Aiano/LocateMagnet/Hardware/114514/PIC/114514.png

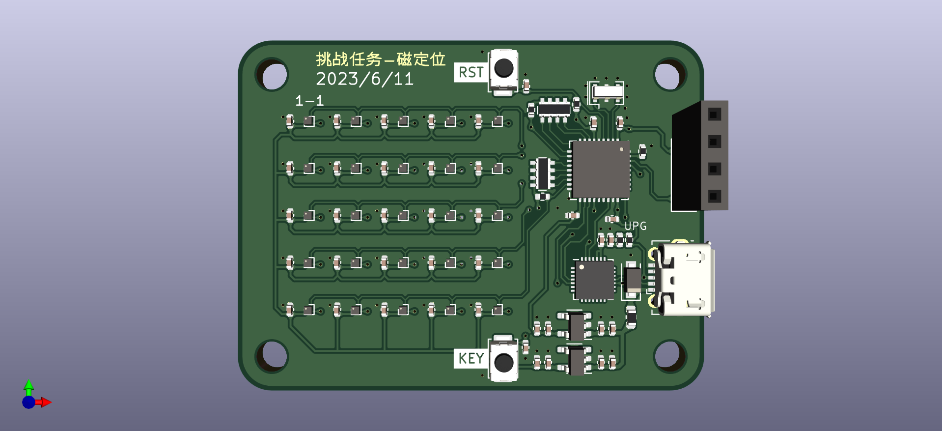
Hardware/114514/PIC/114514.png
