Aiano/LocateMagnet/Hardware/114514/PIC/1145141.png

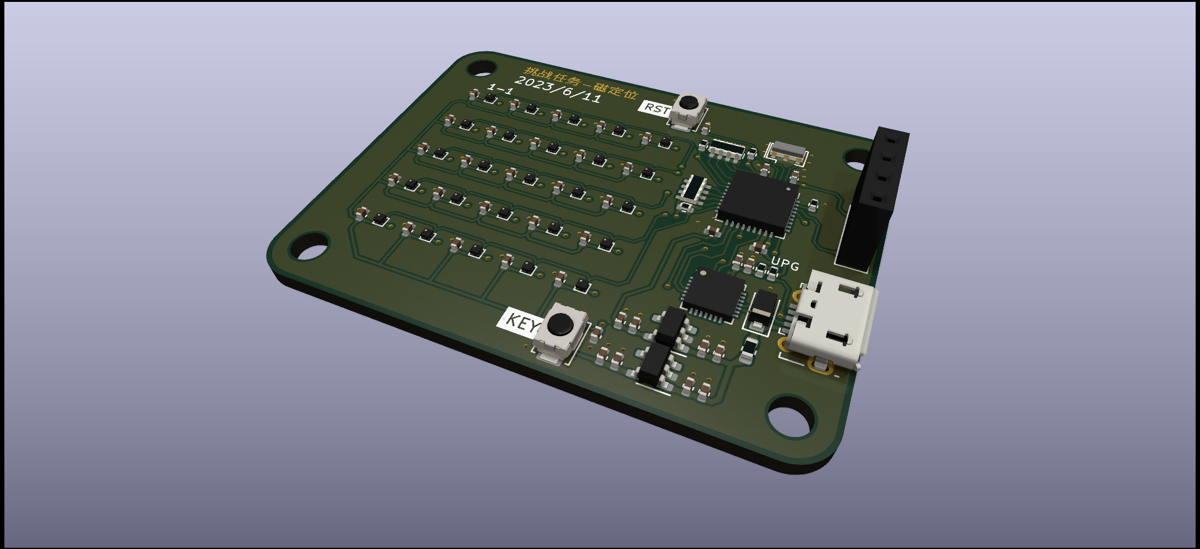
Hardware/114514/PIC/1145141.png
