Aiano/LocateMagnet/Result/反向.png

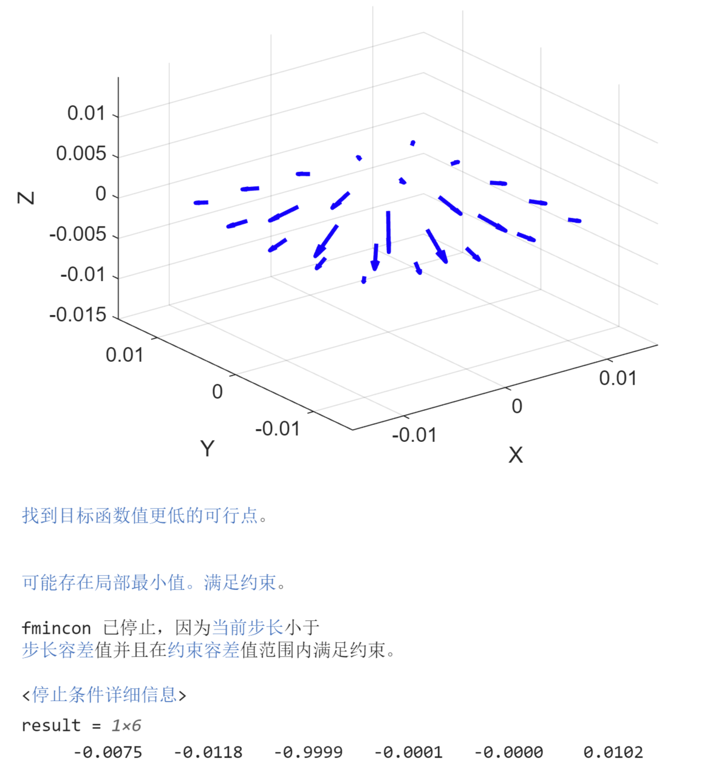
Result/反向.png
