Aiano/LocateMagnet/Result/反向摆放.jpg

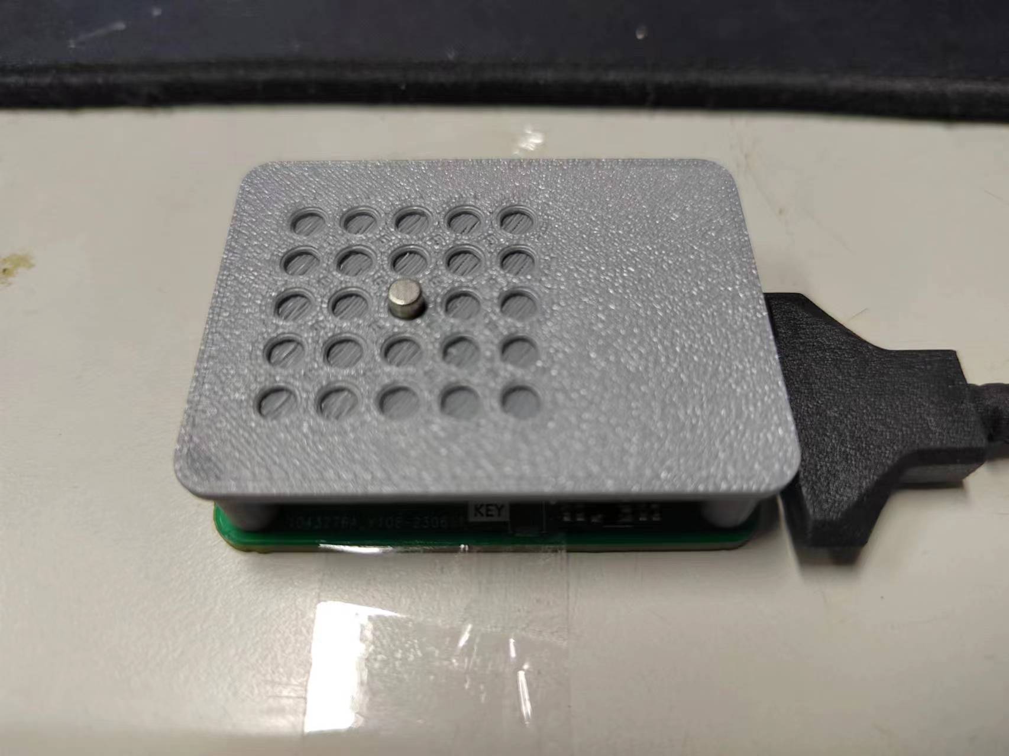
Result/反向摆放.jpg
