Aiano/LocateMagnet/Result/右移0.5mm.png

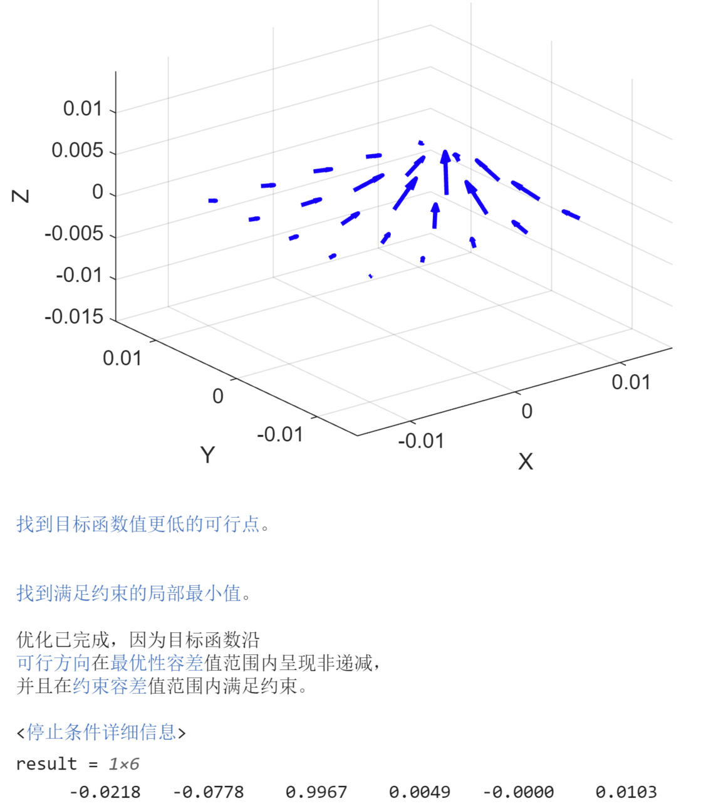
Result/右移0.5mm.png
