Aiano/LocateMagnet/Result/右移0.5mm摆放.jpg

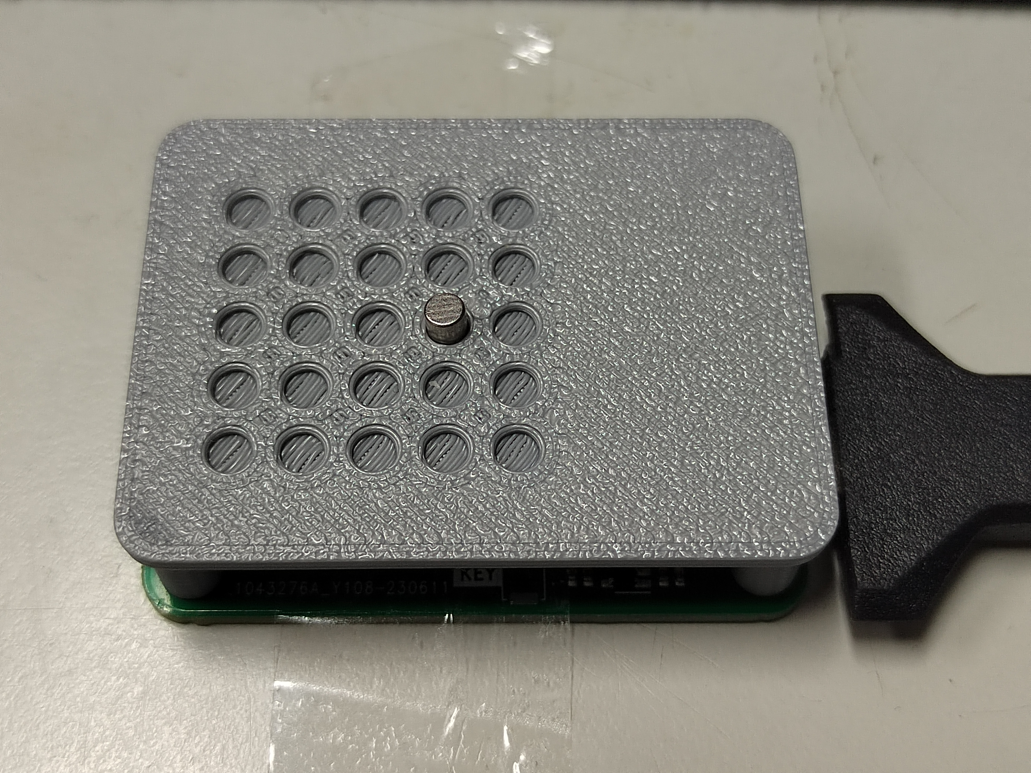
Result/右移0.5mm摆放.jpg
