Aiano/LocateMagnet/Result/右移1mm上移1mm.png

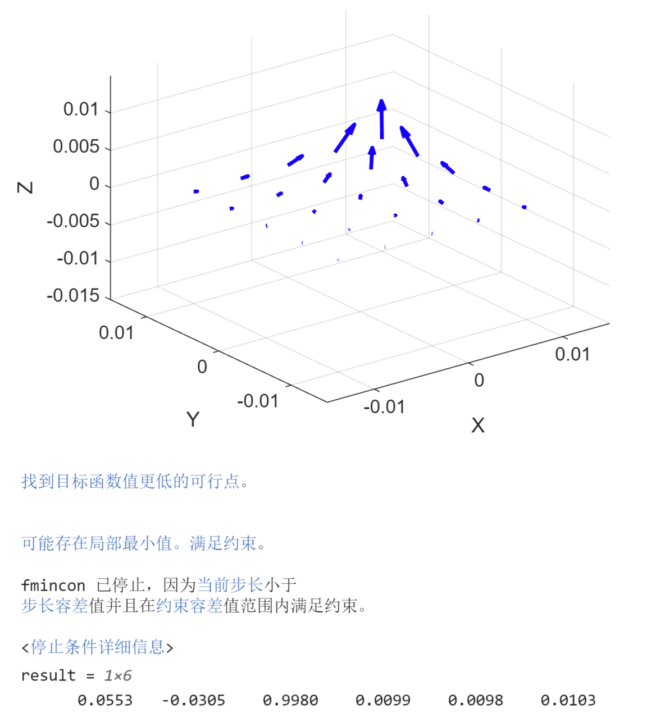
Result/右移1mm上移1mm.png
