Aiano/LocateMagnet/Result/右移1mm上移1mm摆放.jpg

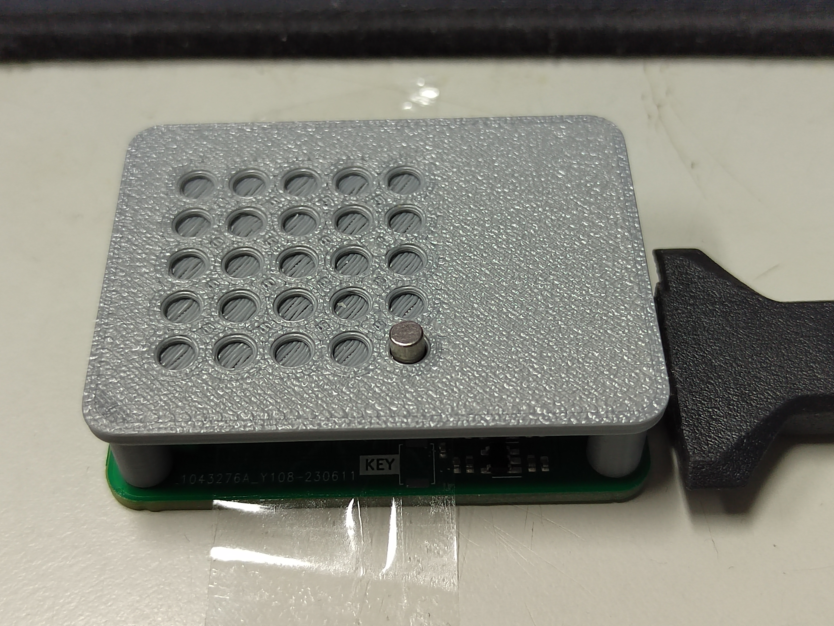
Result/右移1mm上移1mm摆放.jpg
